sowbug/tqw/photos/board.jpg

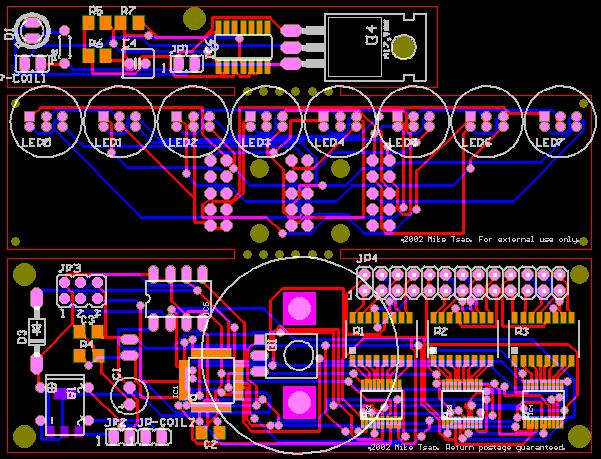
photos/board.jpg
