sowbug/tqw/photos/board_sm.gif

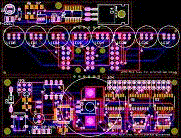
photos/board_sm.gif
