sowbug/tqw/photos/pcb_big.jpg

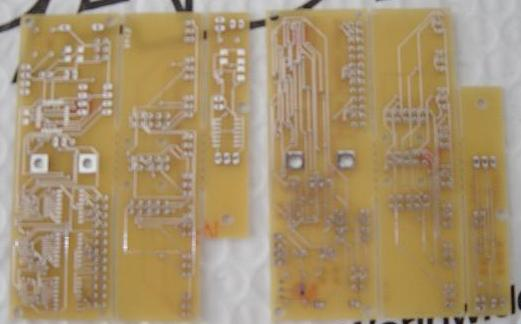
photos/pcb_big.jpg
