sowbug/tqw/photos/side.jpg

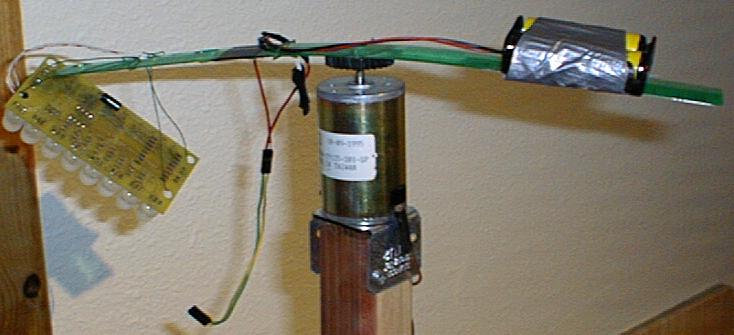
photos/side.jpg
