sowbug/tqw/photos/tqw_side.gif

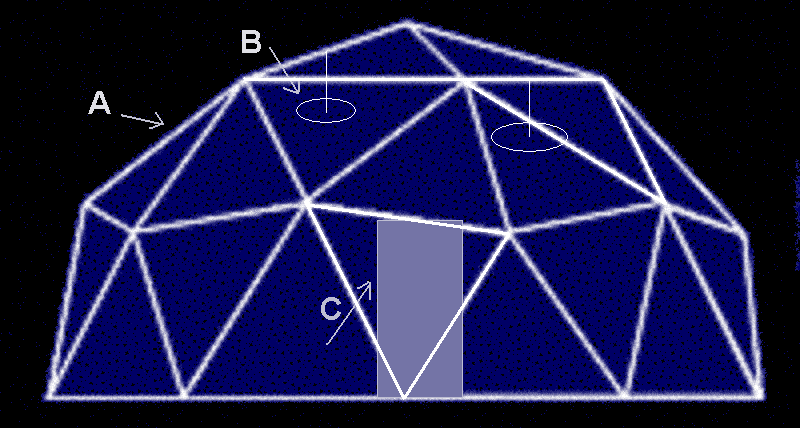
photos/tqw_side.gif
