sowbug/tqw/photos/tqw_side_lg.gif

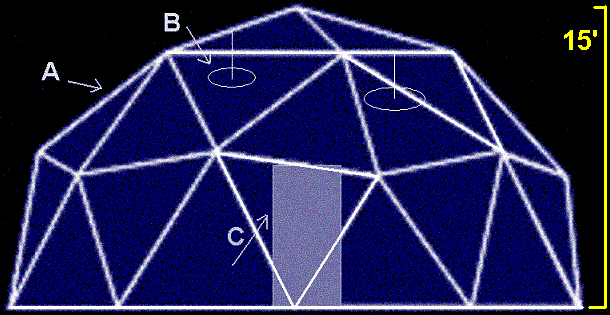
photos/tqw_side_lg.gif
