sowbug/tqw/photos/working_bright.jpg

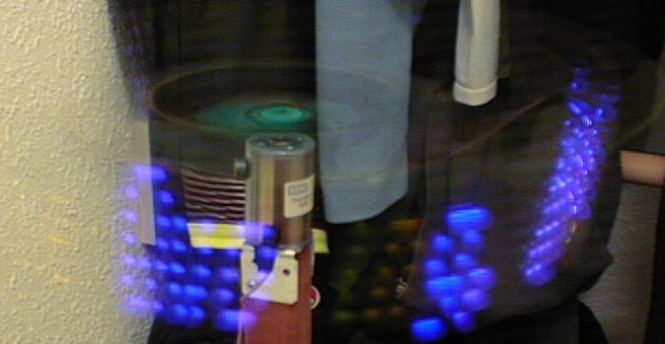
photos/working_bright.jpg
