sowbug/tqw/photos/working_dim.jpg

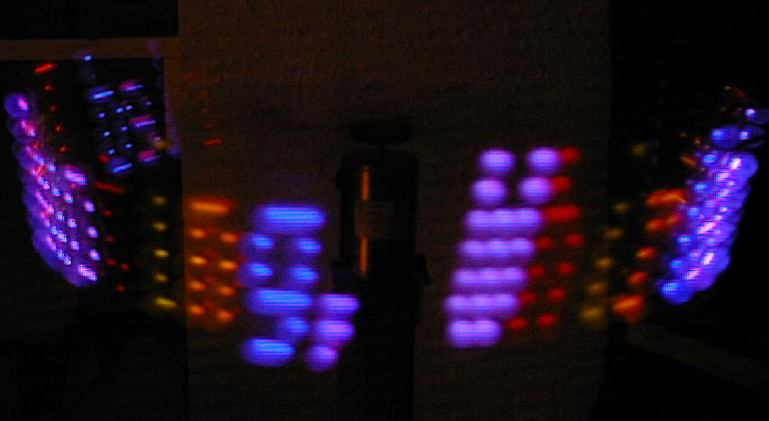
photos/working_dim.jpg
